sh123/esp32_loraprs/extras/images/amp.png

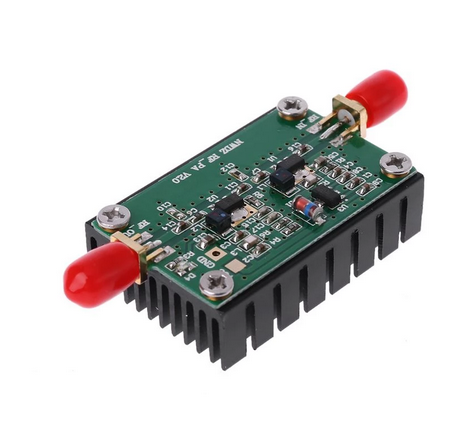
extras/images/amp.png
