sh123/esp32_loraprs/extras/images/aprs_position.png

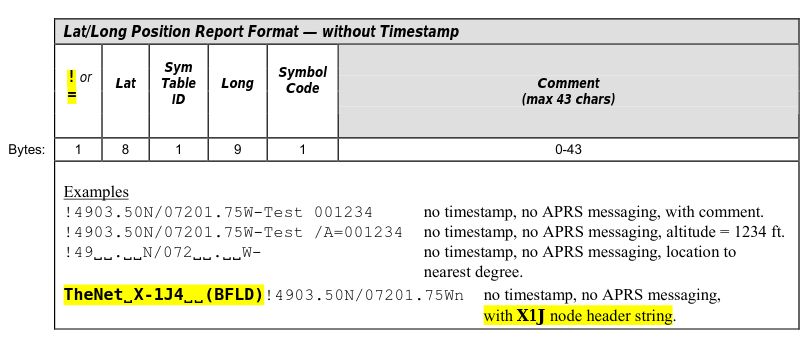
extras/images/aprs_position.png
