sh123/esp32_loraprs/extras/images/aprsdroid.png

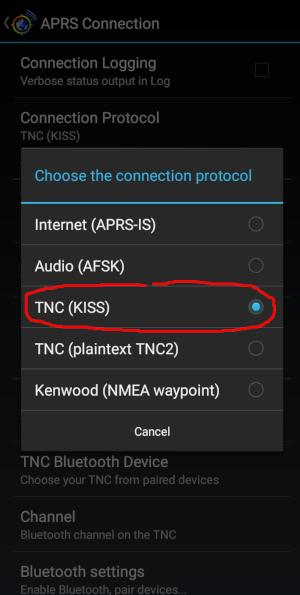
extras/images/aprsdroid.png
