sh123/esp32_loraprs/extras/images/aprsdroid_tnc2.png

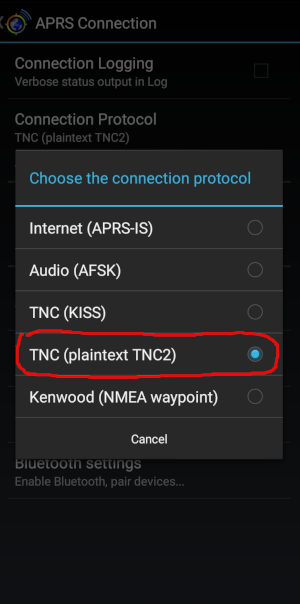
extras/images/aprsdroid_tnc2.png
