sh123/esp32_loraprs/extras/images/codecmode.png

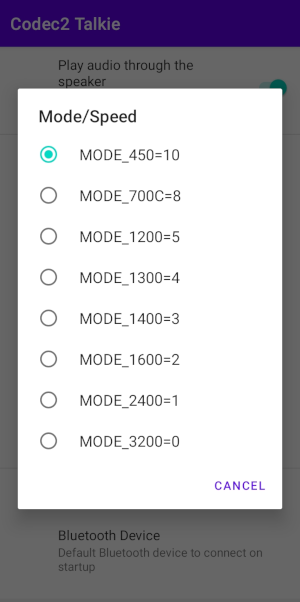
extras/images/codecmode.png
