sh123/esp32_loraprs/extras/images/enable_extensions.png

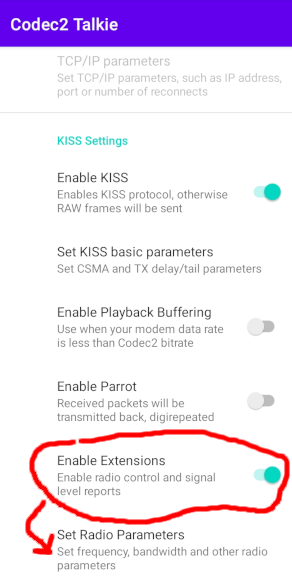
extras/images/enable_extensions.png
