sh123/esp32_loraprs/extras/images/esp32_38pin.jpg

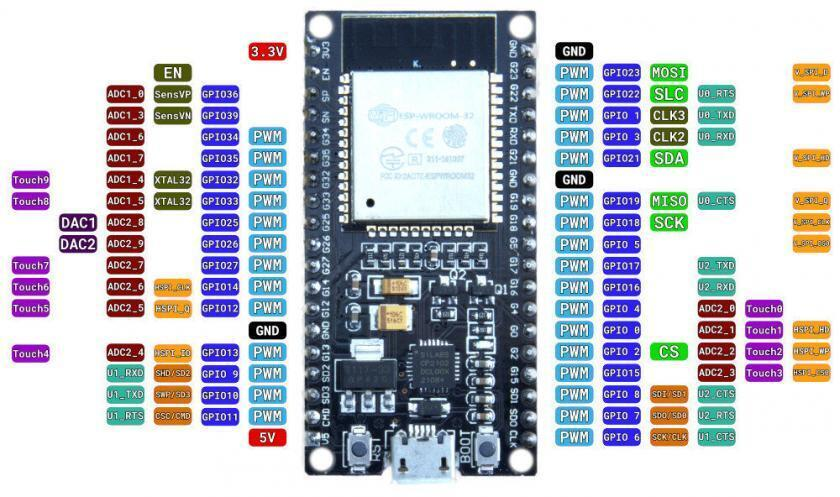
extras/images/esp32_38pin.jpg
