sh123/esp32_loraprs/extras/images/lora_settings.png

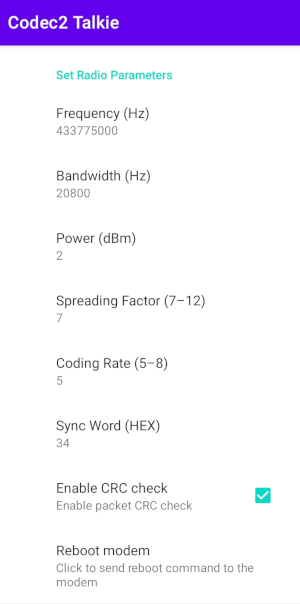
extras/images/lora_settings.png
