sh123/esp32_loraprs/extras/images/rf_vs_c2.png

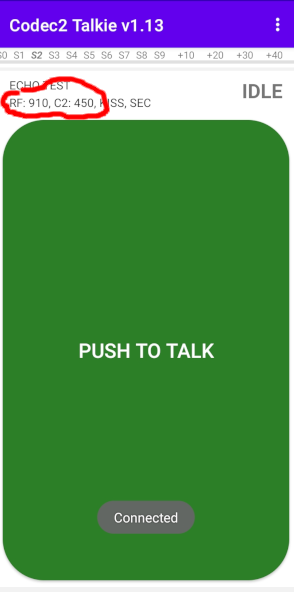
extras/images/rf_vs_c2.png
