sh123/esp32_loraprs/extras/images/s_meter.png

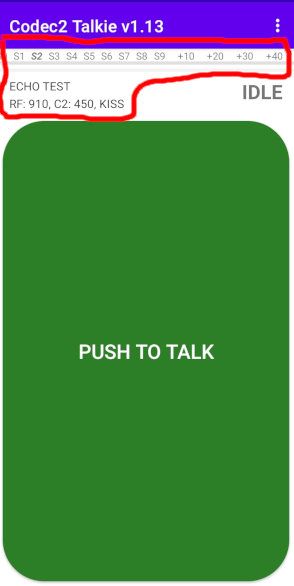
extras/images/s_meter.png
