sh123/esp32_loraprs/extras/images/sx1268.jpg

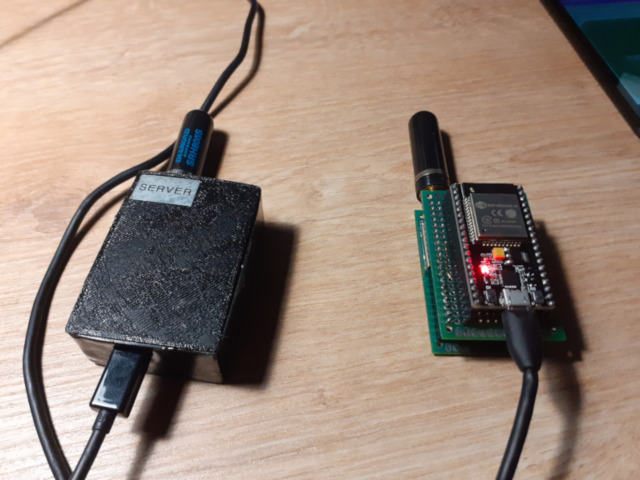
extras/images/sx1268.jpg
