sh123/esp32_loraprs/extras/images/talkie.png

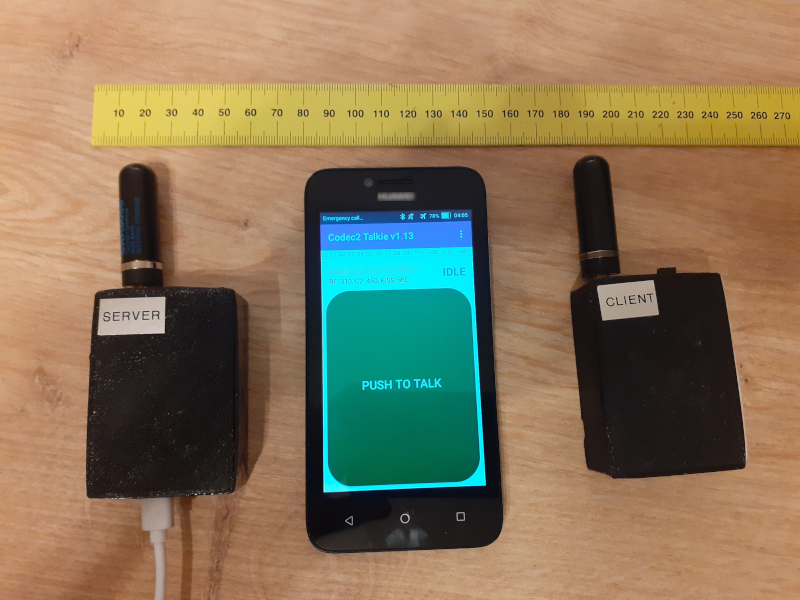
extras/images/talkie.png
