sh123/esp32_loraprs/extras/images/setup.png

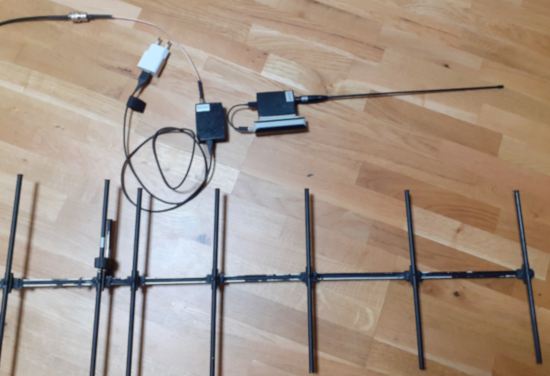
extras/images/setup.png
