sh123/esp32_loraprs/extras/images/solder_pads_38pin.jpg

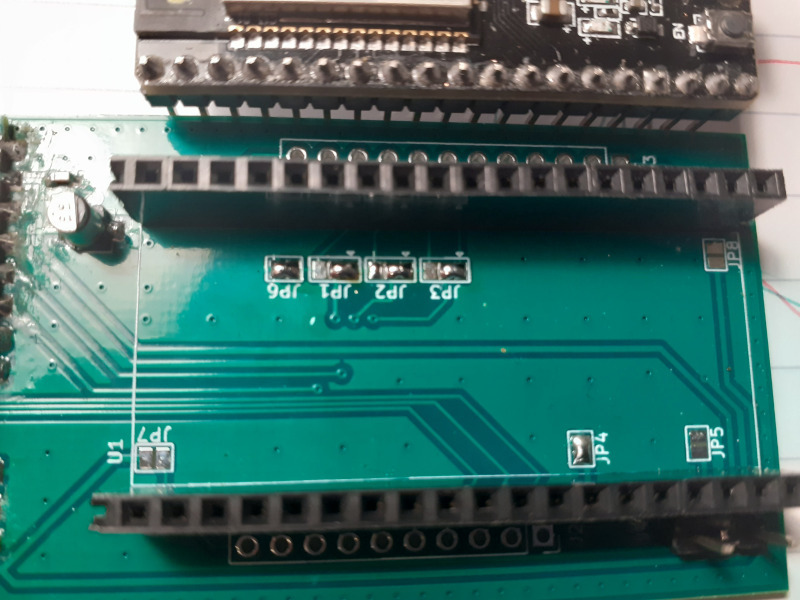
extras/images/solder_pads_38pin.jpg
