sh123/esp32_loraprs/extras/meshcore/loraprs_esp32c3_e22/target.h

#pragma once

#define RADIOLIB_STATIC_ONLY 1
#include <RadioLib.h>
#include <helpers/radiolib/RadioLibWrappers.h>
#include <helpers/ESP32Board.h>
#include <helpers/radiolib/CustomSX1262Wrapper.h>
#include <helpers/radiolib/CustomSX1268Wrapper.h>
#include <helpers/AutoDiscoverRTCClock.h>
#include <helpers/SensorManager.h>

extern ESP32Board board;
extern WRAPPER_CLASS radio_driver;
extern AutoDiscoverRTCClock rtc_clock;
extern SensorManager sensors;

bool radio_init();
uint32_t radio_get_rng_seed();
void radio_set_params(float freq, float bw, uint8_t sf, uint8_t cr);
void radio_set_tx_power(uint8_t dbm);
mesh::LocalIdentity radio_new_identity();
